stephlovesfries/CMOD-A7-2D/uartx.v

`timescale 1ns / 1ps
//////////////////////////////////////////////////////////////////////////////////
// Company: 
// Engineer: 
// 
// Create Date: 13.04.2024 11:08:55
// Design Name: 
// Module Name: uartx
// Project Name: 
// Target Devices: 
// Tool Versions: 
// Description: 
// 
// Dependencies: 
// 
// Revision:
// Revision 0.01 - File Created
// Additional Comments:
// 
//////////////////////////////////////////////////////////////////////////////////


module uart_tx(
    input   clk,
    input   ap_rstn,
    input   ap_ready,
    output  reg ap_vaild,
    output  reg tx,
    input   pairty,
    input  [7:0] data
);

localparam  FSM_IDLE = 3'b000,
            FSM_STAR = 3'b001,
            FSM_TRSF = 3'b010,
            FSM_STOP = 3'b011;
            

reg [2:0] fsm_statu;
reg [2:0] fsm_next;
reg [2:0] cnter;
reg [1:0] byte_cntr;

//fsm start transfer;
always @(posedge clk, negedge ap_rstn) begin
    if (!ap_rstn)begin
        fsm_statu <= FSM_IDLE;
    end else begin
        fsm_statu <= fsm_next;
    end
end

//fsm conditional transfer;
always @(*)begin
    if(!ap_rstn)begin
        fsm_next <= FSM_IDLE;
    end else begin
        case(fsm_statu)
            FSM_IDLE:begin 
                fsm_next <= (ap_ready) ? FSM_STAR : FSM_IDLE;
                byte_cntr <= 0;
            end
            FSM_STAR: begin
                fsm_next <= FSM_TRSF;
                byte_cntr <= byte_cntr + 1;
            end
            FSM_TRSF:begin 
                //fsm_next <= (cnter == 3'h7) ? (pairty?FSM_PARI:FSM_STOP) : FSM_TRSF;
                fsm_next <= (cnter == 3'h7) ? FSM_STOP : FSM_TRSF;
            end
            FSM_STOP:begin 
                fsm_next <= (!ap_ready) ? byte_cntr < 4 ? FSM_STAR :FSM_IDLE : FSM_STOP;
            end
            default: fsm_next <= FSM_IDLE;
        endcase
    end
end
//fsm - output
always @(posedge clk, negedge ap_rstn)begin
    if(!ap_rstn)begin
        ap_vaild <= 1'b0;
        tx <= 1'b1;
    end else begin
        case (fsm_statu)
            FSM_IDLE: begin 
                tx <= 1'b1;
            end
            FSM_STAR: begin 
                ap_vaild <= 1'b0;
                tx <= 1'b0;
                cnter <= 3'h0;
            end
            FSM_TRSF: begin
                tx <= data[cnter];
                cnter <= cnter + 1'b1;
            end
            //FSM_PARI: tx <= (^data); //Parity Check - ODD Check;
            FSM_STOP: begin
                tx <= 1'b1;         //Stop Bit;
                ap_vaild <= 1'b1;
            end
        endcase
    end
end

endmodule
